hannu-hell/Dodge-ESP32-Cam-Tripod/Feet.stl

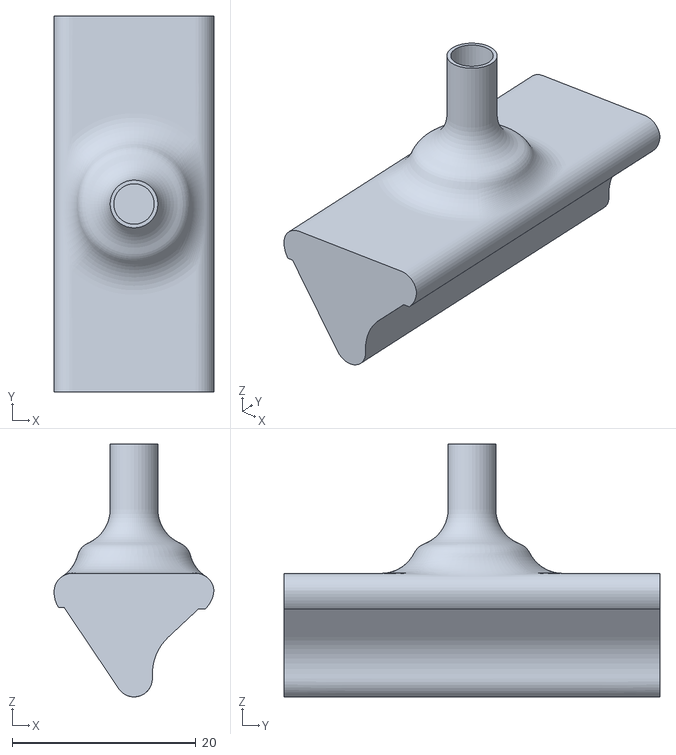
[picture p16: CAD file, 2024-02-05]
Feet.stl
17.4 x 40.9 x 27.5
