hannu-hell/Dodge-ESP32-Cam-Tripod/Coupler_Gear.stl

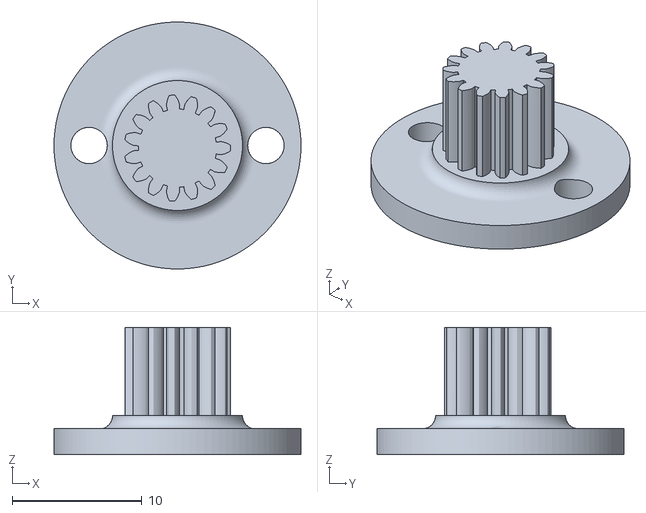
[picture p17: CAD file, 2024-02-05]
Coupler_Gear.stl
19.0 x 19.0 x 9.80
