hannu-hell/Dodge-ESP32-Cam-Tripod/Lower_Leg.stl

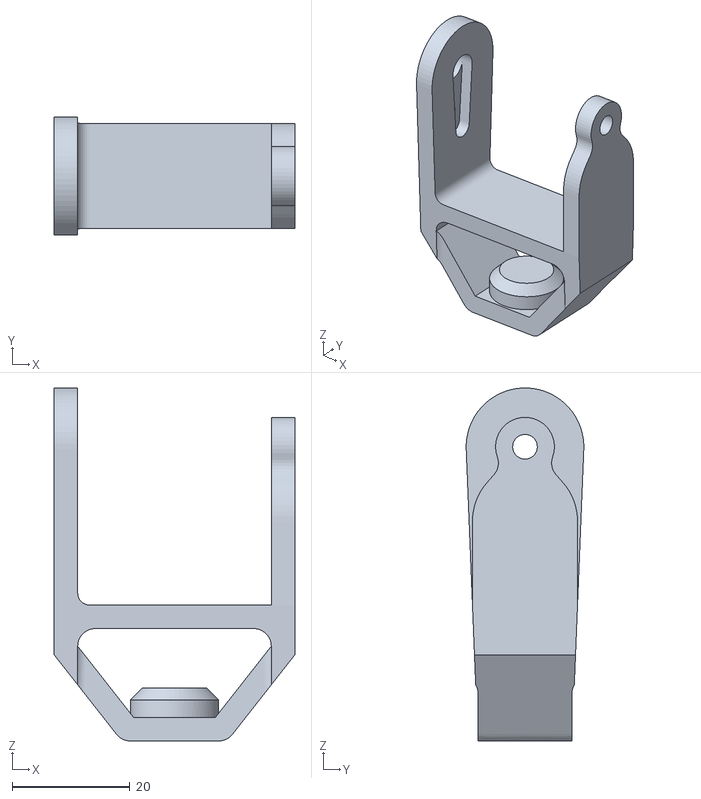
[picture p18: CAD file, 2024-02-05]
Lower_Leg.stl
40.9 x 20.0 x 60.0
