hannu-hell/Dodge-ESP32-Cam-Tripod/Primary_Battery_Compartment.stl

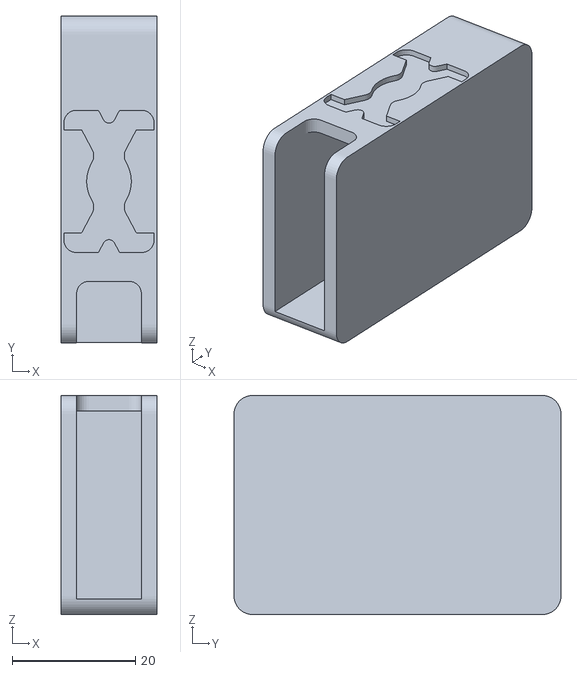
[picture p19: CAD file, 2024-02-05]
Primary_Battery_Compartment.stl
15.5 x 53.0 x 35.5
